ericmcdaniel/wedding-keepsake/src/engine/marquee.cpp

// #include "engine/marquee.h"

// using namespace Engine;

// void Marquee::displayNumber(uint16_t number)
// {
//   // uint8_t digits[5];
//   // uint8_t count = 0;

//   // while (number > 0)
//   // {
//   //   digits[count++] = number % 10;
//   //   number /= 10;
//   // }

//   if (number > 9)
//     return; // TODO: revisit for multiple digit.
// }
